johflo/Seeed-LoRa-E5_BME680/Seeed_Wioe5_BME680/Core/Inc/main.h

#define RTC_N_PREDIV_S 10
#define RTC_PREDIV_S ((1<<RTC_N_PREDIV_S)-1)
#define RTC_PREDIV_A ((1<<(15-RTC_N_PREDIV_S))-1)
#define DBG3_Pin GPIO_PIN_3
#define DBG3_GPIO_Port GPIOB
#define DBG4_Pin GPIO_PIN_4
#define DBG4_GPIO_Port GPIOB
#define USARTx_RX_Pin GPIO_PIN_7
#define USARTx_RX_GPIO_Port GPIOB
#define DBG1_Pin GPIO_PIN_0
#define DBG1_GPIO_Port GPIOA
#define USARTx_TX_Pin GPIO_PIN_6
#define USARTx_TX_GPIO_Port GPIOB
#define DBG2_Pin GPIO_PIN_10
#define DBG2_GPIO_Port GPIOB
#define RF_CTRL1_Pin GPIO_PIN_4
#define RF_CTRL1_GPIO_Port GPIOA
#define RF_CTRL2_Pin GPIO_PIN_5
#define RF_CTRL2_GPIO_Port GPIOA
