johflo/Seeed-LoRa-E5_BME680/Seeed_Wioe5_BME680/Drivers/BME680/common.h

/**
 * Copyright (C) 2021 Bosch Sensortec GmbH. All rights reserved.
 *
 * SPDX-License-Identifier: BSD-3-Clause
 */

#ifdef __cplusplus
extern "C" {
#endif /*__cplusplus */

#include "bme68x.h"


#define I2C_HANDLE	(hi2c3)
#define UART_HANDLE	(huart1)
#define BUS_TIMEOUT             1000
#define DEBUG_EN


/*!
 *  @brief Function to select the interface between SPI and I2C.
 *
 *  @param[in] bme      : Structure instance of bme68x_dev
 *  @param[in] intf     : Interface selection parameter
 *
 *  @return Status of execution
 *  @retval 0 -> Success
 *  @retval < 0 -> Failure Info
 */
int8_t bme68x_interface_init(struct bme68x_dev *bme, uint8_t intf);

/*!
 *  @brief Function for reading the sensor's registers through I2C bus.
 *
 *  @param[in] reg_addr     : Register address.
 *  @param[out] reg_data    : Pointer to the data buffer to store the read data.
 *  @param[in] len          : No of bytes to read.
 *  @param[in] intf_ptr     : Interface pointer
 *
 *  @return Status of execution
 *  @retval = BME68X_INTF_RET_SUCCESS -> Success
 *  @retval != BME68X_INTF_RET_SUCCESS  -> Failure Info
 *
 */
BME68X_INTF_RET_TYPE bme68x_i2c_read(uint8_t reg_addr, uint8_t *reg_data, uint32_t len, void *intf_ptr);

/*!
 *  @brief Function for writing the sensor's registers through I2C bus.
 *
 *  @param[in] reg_addr     : Register address.
 *  @param[in] reg_data     : Pointer to the data buffer whose value is to be written.
 *  @param[in] len          : No of bytes to write.
 *  @param[in] intf_ptr     : Interface pointer
 *
 *  @return Status of execution
 *  @retval = BME68X_INTF_RET_SUCCESS -> Success
 *  @retval != BME68X_INTF_RET_SUCCESS  -> Failure Info
 *
 */
BME68X_INTF_RET_TYPE bme68x_i2c_write(uint8_t reg_addr, const uint8_t *reg_data, uint32_t len, void *intf_ptr);



/*!
 * @brief This function provides the delay for required time (Microsecond) as per the input provided in some of the
 * APIs.
 *
 *  @param[in] period       : The required wait time in microsecond.
 *  @param[in] intf_ptr     : Interface pointer
 *
 *  @return void.
 *
 */
void bme68x_delay_us(uint32_t period, void *intf_ptr);

/*!
 *  @brief Prints the execution status of the APIs.
 *
 *  @param[in] api_name : Name of the API whose execution status has to be printed.
 *  @param[in] rslt     : Error code returned by the API whose execution status has to be printed.
 *
 *  @return void.
 */
void bme68x_check_rslt(const char api_name[], int8_t rslt);

void DelayUs(uint32_t Delay);
void UART_Printf(uint8_t* buff, uint16_t size);
void PDEBUG(char *format, ...);

#ifdef __cplusplus
}
#endif /*__cplusplus */
